marchingband/wvr_hardware/images/gui_firmware.png

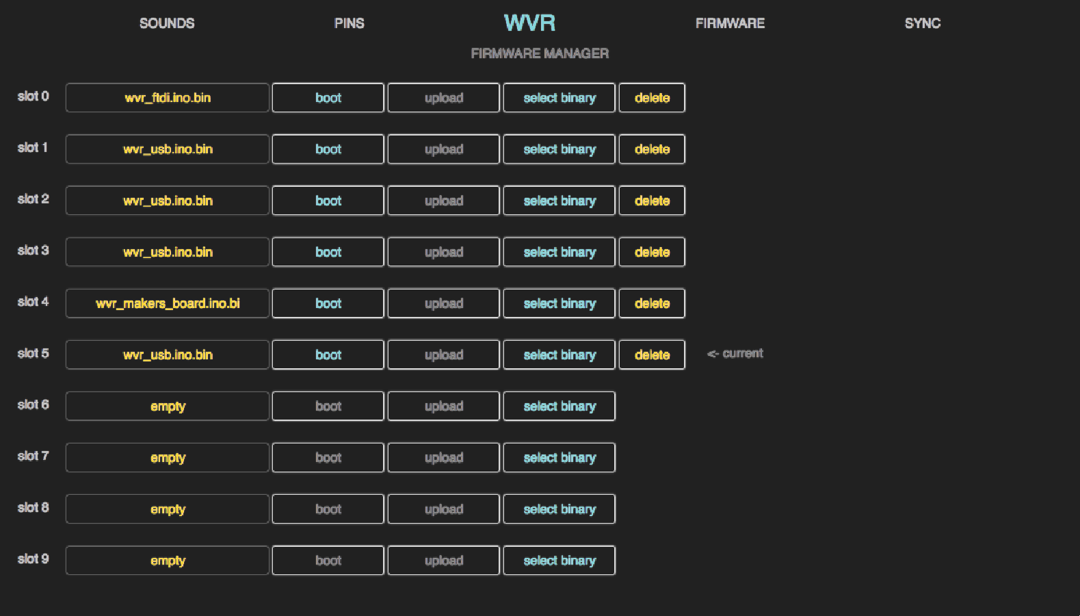
images/gui_firmware.png
