marchingband/wvr_hardware/images/gui_sounds.png

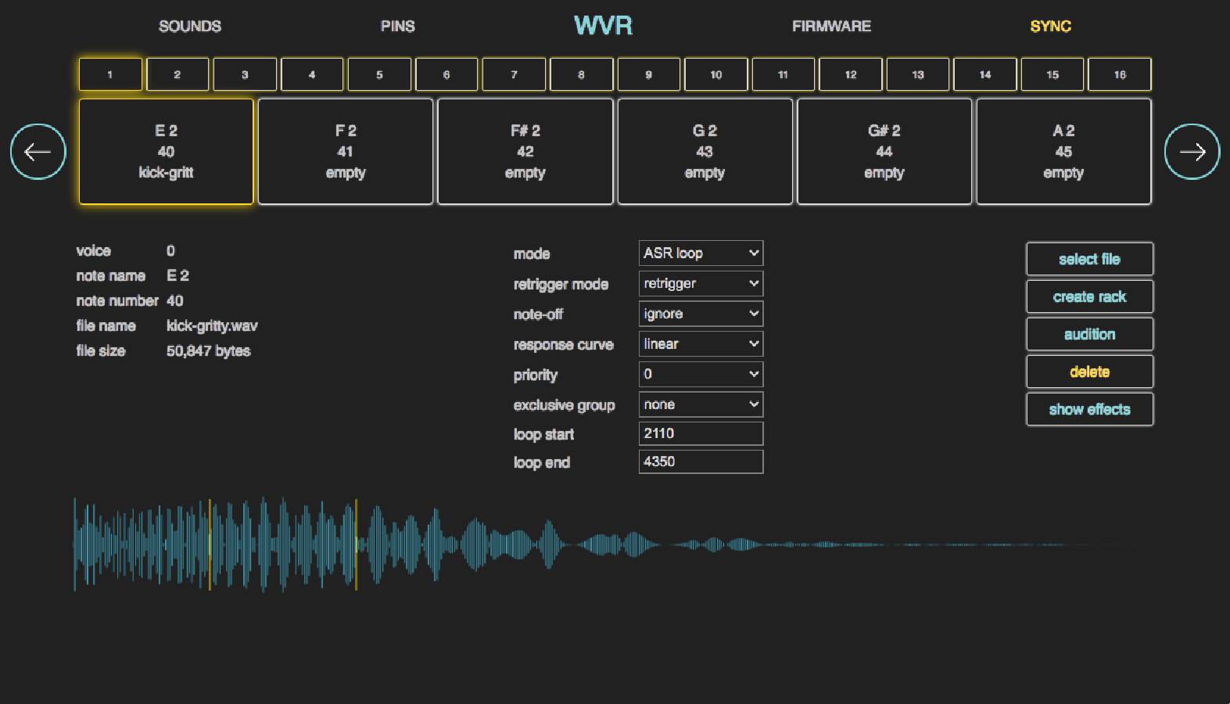
images/gui_sounds.png
